StePol/MultiChannel_datalogger/hardware/schematic/MultiChannel_datalogger.kicad_sch

## KiCad design hardware/schematic/MultiChannel_datalogger.kicad_sch (2026-10-01, an earlier design)

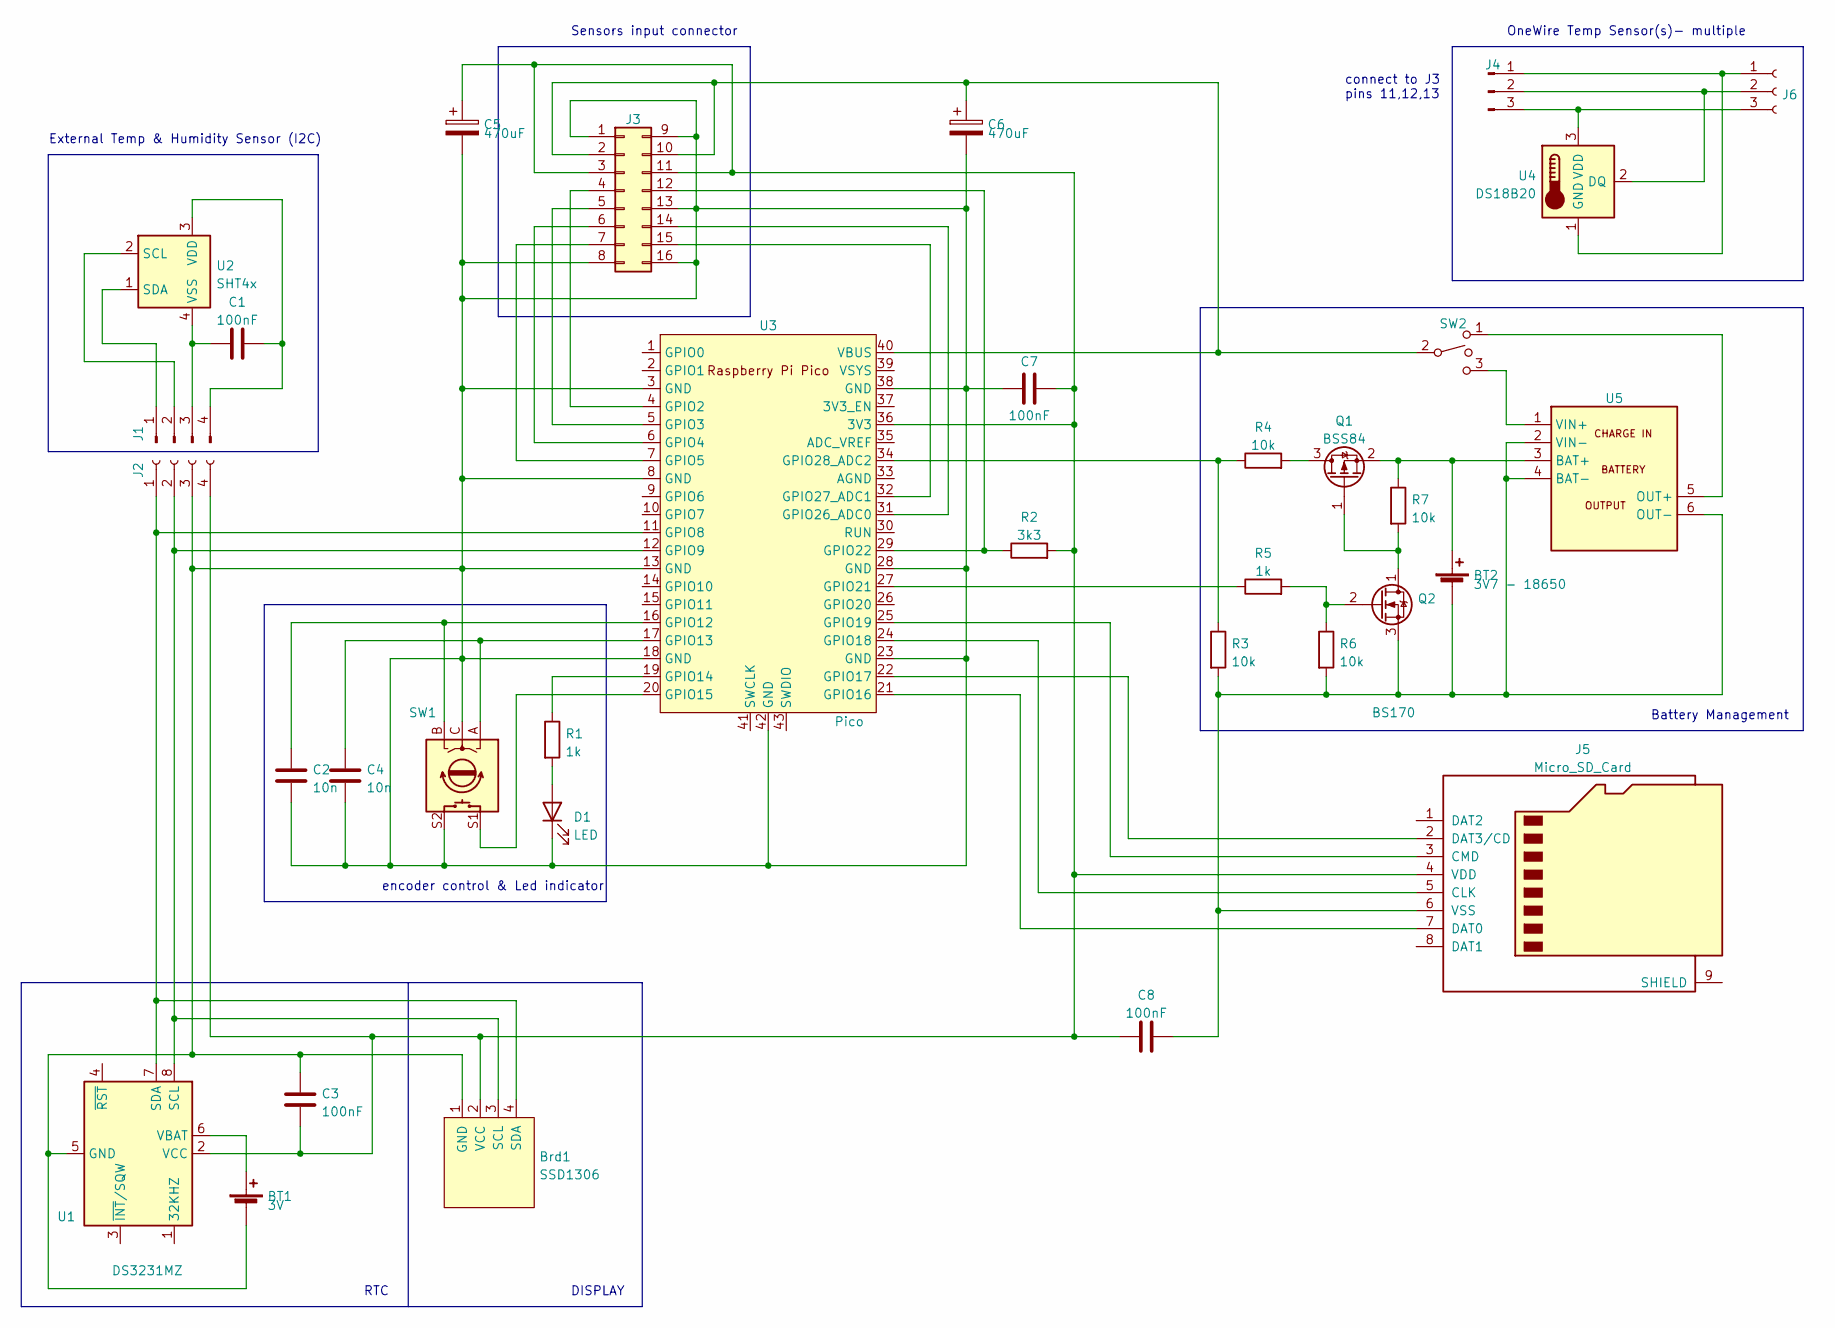
[picture p2: schematic MultiChannel_datalogger.kicad_sch]

Parts:
BT1: 3V
BT2: 3V7 - 18650
Brd1: SSD1306
C1, C3, C7, C8: 100nF
C2, C4: 10n
C5, C6: 470uF
D1: LED
J1: Conn_01x04_Male
J2: Conn_01x04_Female
J3: Conn_02x08_Top_Bottom
J4: Conn_01x03_Male
J5: Micro_SD_Card
J6: Conn_01x03_Female
Q1: BSS84; SOT-23
Q2: BS170; TO-92_Inline
R1, R5: 1k
R2: 3k3
R3, R4, R6, R7: 10k
SW1: RotaryEncoder_Switch
SW2: SW_SPDT_MSM
U1: DS3231MZ; SOIC-8_3.9x4.9mm_P1.27mm
U2: SHT4x; Sensirion_DFN-4_1.5x1.5mm_P0.8mm_SHT4x_NoCentralPad
U3: Pico; RPi_Pico_SMD_TH
U4: DS18B20; TO-92_Inline
U5: 18650_Boost_TypeC_Module

Connections:
unnamed: BT1.1 (+), U1.6 (VBAT)
unnamed: BT1.2 (-), Brd1.1 (GND), C2.2, C3.1, C4.2, C5.2, C6.2, C7.1, D1.1 (K), J2.3, J3.1, J3.8, J3.9, J3.13, J3.16, SW1.C, SW1.S2, U1.5 (GND), U3.3 (GND), U3.8 (GND), U3.13 (GND), U3.18 (GND), U3.23 (GND), U3.28 (GND), U3.38 (GND), U3.42 (GND)
unnamed: BT2.1 (+), Q1.2 (S), R7.1, U5.3 (BAT+)
unnamed: BT2.2 (-), C8.2, J5.6 (VSS), Q2.3 (S), R3.2, R6.2, U5.2 (VIN-), U5.4 (BAT-), U5.6 (OUT-)
unnamed: Brd1.2 (VCC), C3.2, C5.1, C7.2, C8.1, J2.4, J3.3, J3.11, J5.4 (VDD), R2.2, U1.2 (VCC), U3.36 (3V3)
unnamed: Brd1.3 (SCL), J2.2, U1.8 (SCL), U3.12 (GPIO9)
unnamed: Brd1.4 (SDA), J2.1, U1.7 (SDA), U3.11 (GPIO8)
unnamed: C1.1, J1.3, U2.4 (VSS)
unnamed: C1.2, J1.4, U2.3 (VDD)
unnamed: C2.1, SW1.B, U3.16 (GPIO12)
unnamed: C4.1, SW1.A, U3.17 (GPIO13)
unnamed: C6.1, J3.2, J3.10, SW2.2, U3.40 (VBUS)
unnamed: D1.2 (A), R1.2
unnamed: J1.1, U2.1 (SDA)
unnamed: J1.2, U2.2 (SCL)
unnamed: J3.4, U3.4 (GPIO2)
unnamed: J3.5, U3.5 (GPIO3)
unnamed: J3.6, U3.6 (GPIO4)
unnamed: J3.7, U3.7 (GPIO5)
unnamed: J3.12, R2.1, U3.29 (GPIO22)
unnamed: J3.14, U3.31 (GPIO26_ADC0)
unnamed: J3.15, U3.32 (GPIO27_ADC1)
unnamed: J4.1, J6.1, U4.1 (GND)
unnamed: J4.2, J6.2, U4.2 (DQ)
unnamed: J4.3, J6.3, U4.3 (VDD)
unnamed: J5.2 (DAT3/CD), U3.22 (GPIO17)
unnamed: J5.3 (CMD), U3.25 (GPIO19)
unnamed: J5.5 (CLK), U3.24 (GPIO18)
unnamed: J5.7 (DAT0), U3.21 (GPIO16)
unnamed: Q1.1 (G), Q2.1 (D), R7.2
unnamed: Q1.3 (D), R4.2
unnamed: Q2.2 (G), R5.2, R6.1
unnamed: R1.1, U3.19 (GPIO14)
unnamed: R3.1, R4.1, U3.34 (GPIO28_ADC2)
unnamed: R5.1, U3.27 (GPIO21)
unnamed: SW1.S1, U3.20 (GPIO15)
unnamed: SW2.1, U5.5 (OUT+)
unnamed: SW2.3, U5.1 (VIN+)

Notes on the sheet:
Battery Management
connect to J3 pins 11,12,13
DISPLAY
External Temp & Humidity Sensor (I2C)
Sensors input connector
encoder control & Led indicator
OneWire Temp Sensor(s)- multiple
RTC
