StePol/MultiChannel_datalogger/firmware/ssd1306.py

from micropython import const
import framebuf

class SSD1306(framebuf.FrameBuffer):
    def __init__(self, width, height, external_vcc):
        self.width, self.height, self.external_vcc = width, height, external_vcc
        self.buffer = bytearray(self.width * self.height // 8)
        super().__init__(self.buffer, self.width, self.height, framebuf.MONO_VLSB)
        self.init_display()

    def init_display(self):
        for cmd in (0xAE, 0x20, 0x10, 0x40, 0x81, 0xFF, 0xA1, 0xA6, 0xA8, 0x3F, 0xD3, 0x00, 0xD5, 0x80, 0xD9, 0x22, 0xDA, 0x12, 0xDB, 0x20, 0x8D, 0x14, 0xAF):
            self.write_cmd(cmd)

class SSD1306_I2C(SSD1306):
    def __init__(self, width, height, i2c, addr=0x3C, external_vcc=False):
        self.i2c, self.addr = i2c, addr
        self.temp = bytearray(2)
        super().__init__(width, height, external_vcc)

    def write_cmd(self, cmd):
        self.temp[0], self.temp[1] = 0x80, cmd
        self.i2c.writeto(self.addr, self.temp)

    def show(self):
        self.i2c.writeto(self.addr, b'\x40' + self.buffer)
